ECE-196/final-project-team-12/misc files/DW Updates/wireless tested.png

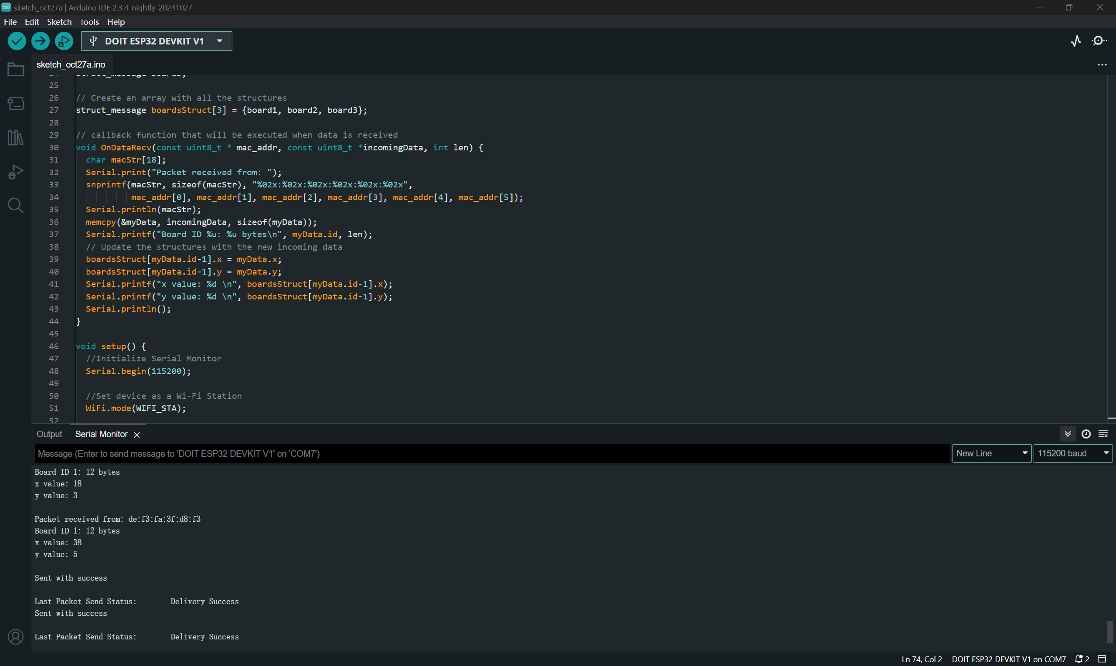
misc files/DW Updates/wireless tested.png
