ECE-196/final-project-team-12/misc files/LiDAR demos/1st LiDAR LD-14P/LD20_SerialTest.ino

struct LidarPointStructDef { 
  uint16_t distance;
  uint8_t intensity;
};

struct LiDARFrame {
  uint8_t header;   // start byte (0x54)
  uint8_t ver_len;
  uint16_t speed;
  uint16_t startangle;
  LidarPointStructDef data[12];
  uint16_t end_angle;
  uint16_t timestamp;
  uint8_t crc8;
};



int dataList[47];

void setup() {
    Serial.begin(230400);   // For Serial Monitor
    Serial1.begin(230400);  // For Serial1 communication
}

void printDatalist(){
  for (int i = 0; i < 47; i++) {
    if(dataList[i] < 16){
      Serial.print("0");
    }
    Serial.print(dataList[i], HEX);
    Serial.print(" ");
  }
  Serial.println();
}


/*
void loop() {
    // Check if data is available on Serial1
    if (Serial1.available()) {
      int incomingByte = Serial1.read();
      if (incomingByte == 84) {     //0x54 is the start byte
        dataList[0] = incomingByte;
        for (int i = 1; i < 47; i++) {
          if (Serial1.available()) {
            dataList[i] = Serial1.read();
          }
        }

      printDatalist();
    }
  }
}
*/

void loop(){
  if (Serial1.available()) {
    Serial.println(Serial1.read(), HEX);
  }
}


/*
54 49 21 2C 10 00 1D 00 75 00 1D 00 1D 00 1D 00 1D 00 1D 00 75 00 75 00 75 00 74 00 60 08 C5 79 54 2C 2F 08 43 00 D4 00 75 00 1D 00 1D 00 1D 
54 E9 21 43 21 00 1D 00 75 00 1D 00 1D 00 1D 00 1D 00 1D 00 75 00 75 00 75 00 74 00 60 59 A8 31 FF 54 E9 21 CC 43 00 1D 00 75 00 1D 00 1D 00 
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
      count = 0;
      Serial.print(incomingByte, HEX);
      Serial.print(" ");

    } else {
      if(incomingByte < 16){
        Serial.print(" ");
      }
      Serial.print(incomingByte, HEX);
      count++;
      Serial.print(" ");
    }
  }
}
*/
